MitchiLaser/Parallax/hardware/afe.kicad_sch

## KiCad design hardware/afe.kicad_sch (2025-06-27)

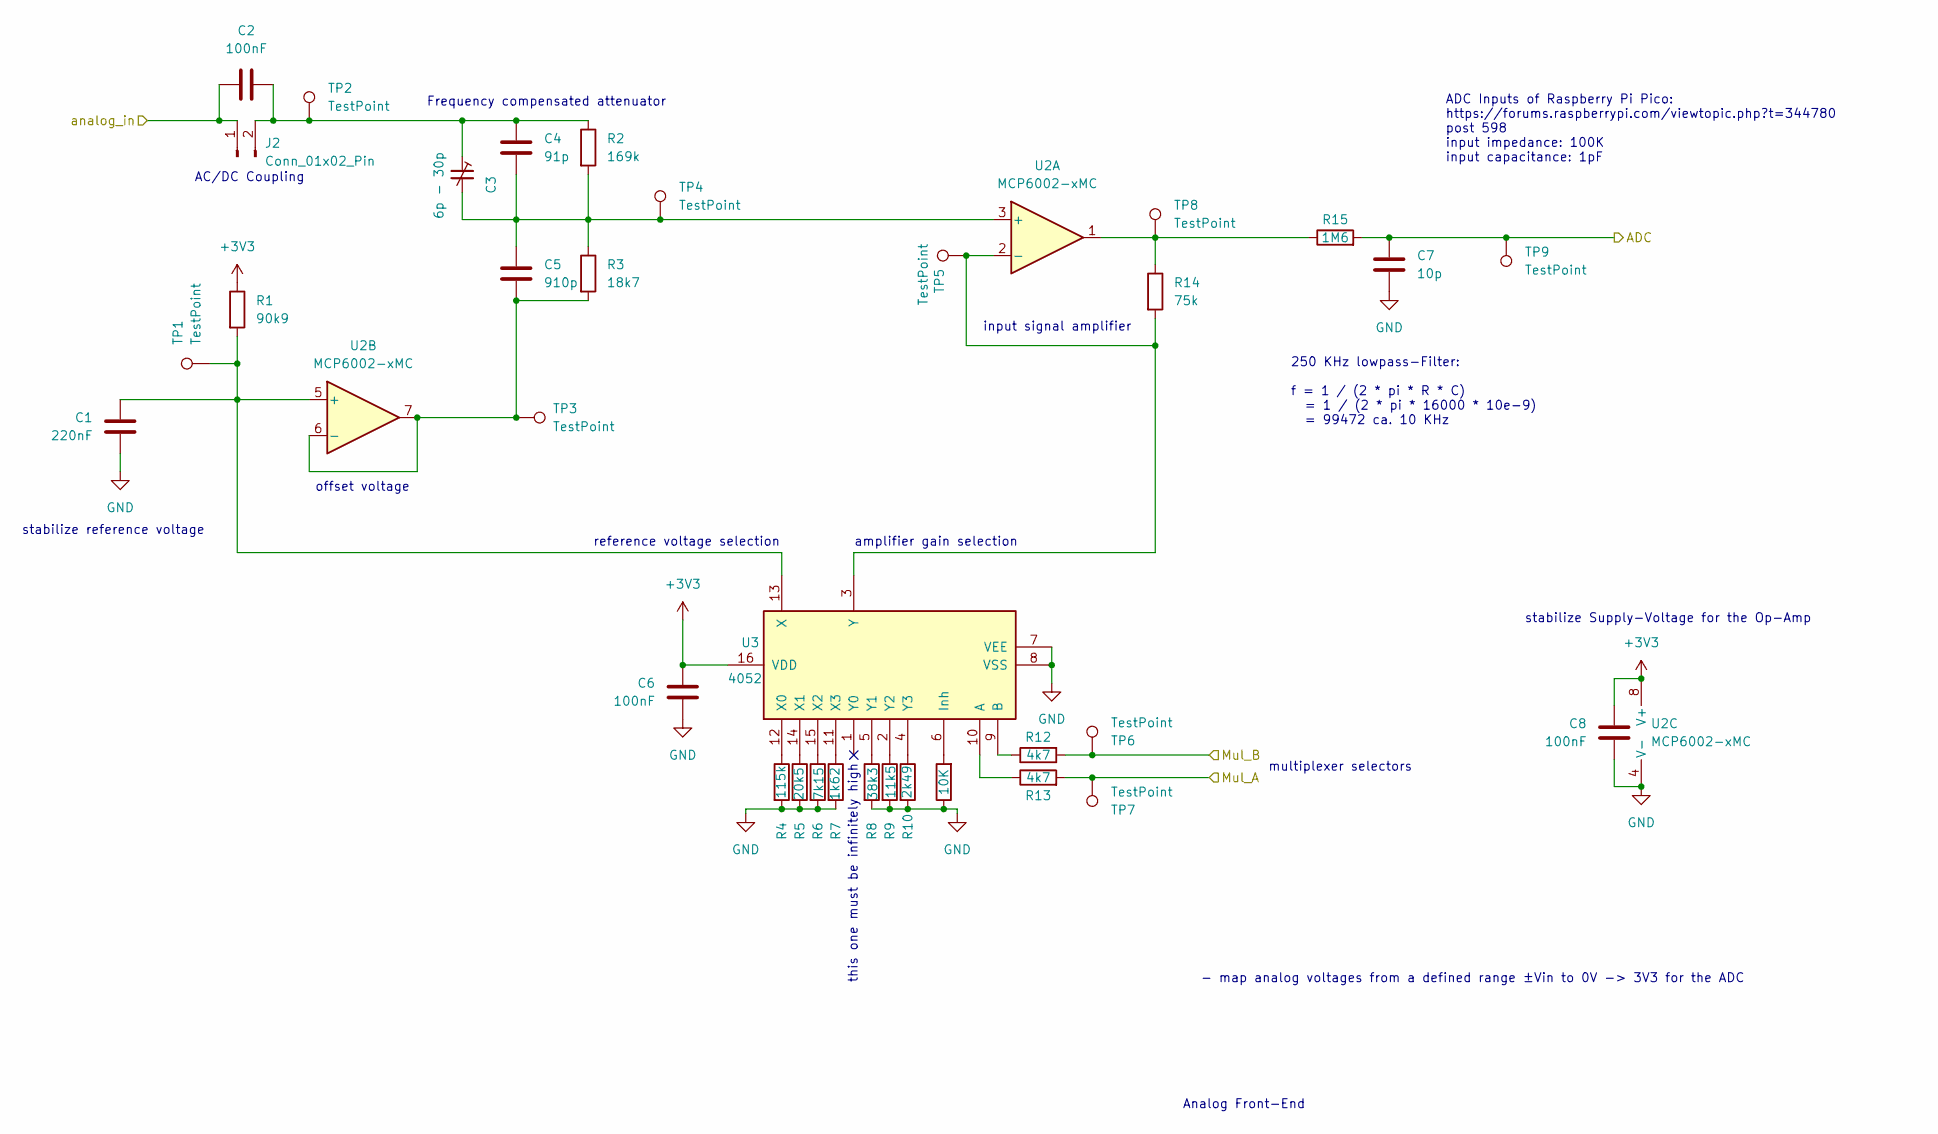
[picture p3: schematic afe.kicad_sch]

Parts:
C1: 220nF; C_0603_1608Metric
C2, C6, C8: 100nF; C_0603_1608Metric
C3: 6p - 30p; c_trim_D6mm_P5mm_1
C4: 91p; C_0603_1608Metric
C5: 910p; C_0603_1608Metric
C7: 10p; C_0603_1608Metric
J2: Conn_01x02_Pin; PinHeader_1x02_P2.54mm_Vertical
R1: 90k9; R_0603_1608Metric
R2: 169k; R_0603_1608Metric
R3: 18k7; R_0603_1608Metric
R4: 115k; R_0603_1608Metric
R5: 20k5; R_0603_1608Metric
R6: 7k15; R_0603_1608Metric
R7: 1k62; R_0603_1608Metric
R8: 38k3; R_0603_1608Metric
R9: 11k5; R_0603_1608Metric
R10: 2k49; R_0603_1608Metric
R11: 10K; R_0603_1608Metric
R12, R13: 4k7; R_0603_1608Metric
R14: 75k; R_0603_1608Metric
R15: 1M6; R_0603_1608Metric
TP1, TP2, TP3, TP4, TP5, TP6, TP7, TP8, TP9: TestPoint; TestPoint_Pad_D1.5mm
U2: MCP6002-xMC; DFN-8-1EP_3x2mm_P0.5mm_EP1.75x1.45mm
U3: 4052; SSOP-16_5.3x6.2mm_P0.65mm

Connections:
+3V3: C6.1, C8.1, R1.1, U2.8 (V+), U3.16 (VDD)
ADC: C7.1, R15.2, TP9.1
GND: C1.2, C6.2, C7.2, C8.2, R4.2, R5.2, R6.2, R7.2, R8.2, R9.2, R10.2, R11.1, U2.4 (V-), U2.9 (V-), U3.7 (VEE), U3.8 (VSS)
Mul_A: R13.2, TP7.1
Mul_B: R12.2, TP6.1
unnamed: C1.1, R1.2, TP1.1, U2.5 (+), U3.13 (X)
unnamed: C2.2, C3.1, C4.1, J2.2, R2.1, TP2.1
unnamed: C3.2, C4.2, C5.1, R2.2, R3.1, TP4.1, U2.3 (+)
unnamed: C5.2, R3.2, TP3.1, U2.6 (-), U2.7
unnamed: R4.1, U3.12 (X0)
unnamed: R5.1, U3.14 (X1)
unnamed: R6.1, U3.15 (X2)
unnamed: R7.1, U3.11 (X3)
unnamed: R8.1, U3.5 (Y1)
unnamed: R9.1, U3.2 (Y2)
unnamed: R10.1, U3.4 (Y3)
unnamed: R11.2, U3.6 (Inh)
unnamed: R12.1, U3.9 (B)
unnamed: R13.1, U3.10 (A)
unnamed: R14.1, R15.1, TP8.1, U2.1
unnamed: R14.2, TP5.1, U2.2 (-), U3.3 (Y)
analog_in: C2.1, J2.1

Notes on the sheet:
offset voltage
250 KHz lowpass-Filter: f = 1 / (2 * pi * R * C) = 1 / (2 * pi * 16000 * 10e-9) = 99472 ca. 10 KHz
- map analog voltages from a defined range ±Vin to 0V -> 3V3 for the ADC
ADC Inputs of Raspberry Pi Pico: https://forums.raspberrypi.com/viewtopic.php?t=344780 post 598 input impedance: 100K input capacitance: 1pF
reference voltage selection
AC/DC Coupling
Frequency compensated attenuator
input signal amplifier
this one must be infinitely high
amplifier gain selection
Analog Front-End
stabilize Supply-Voltage for the Op-Amp
multiplexer selectors
stabilize reference voltage
