MitchiLaser/Parallax/hardware/awg.kicad_sch

## KiCad design hardware/awg.kicad_sch (2025-06-20)

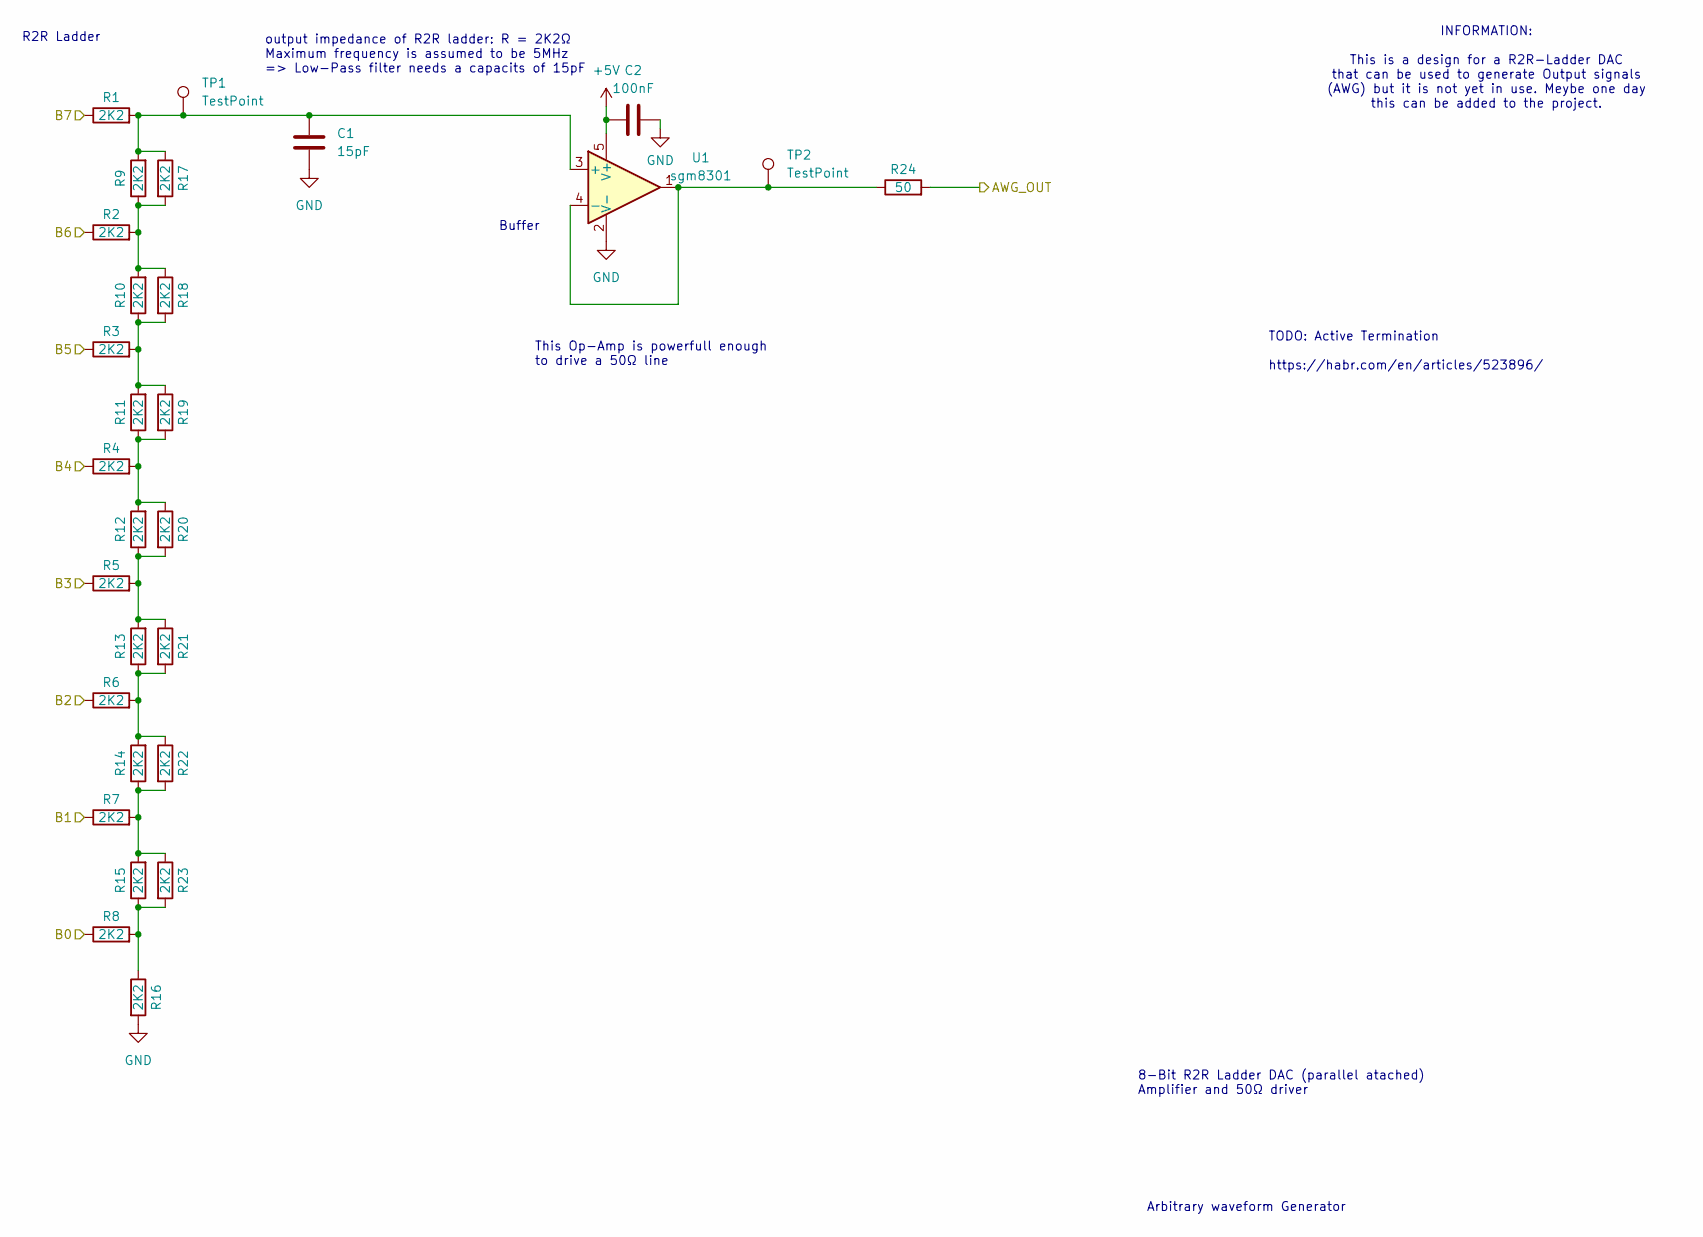
[picture p4: schematic awg.kicad_sch]

Parts:
C1: 15pF; C_0805_2012Metric_Pad1.18x1.45mm_HandSolder
C2: 100nF; C_0805_2012Metric_Pad1.18x1.45mm_HandSolder
R1, R2, R3, R4, R5, R6, R7, R8, R9, R10, R11, R12, R13, R14, R15, R16, R17, R18, R19, R20, R21, R22, R23: 2K2; R_0805_2012Metric_Pad1.20x1.40mm_HandSolder
R24: 50; R_0805_2012Metric_Pad1.20x1.40mm_HandSolder
TP1, TP2: TestPoint; TestPoint_Pad_D1.5mm
U1: sgm8301; SOT-23-5

Connections:
+5V: C2.1, U1.5 (V+)
AWG_OUT: R24.2
B0: R8.1
B1: R7.1
B2: R6.1
B3: R5.1
B4: R4.1
B5: R3.1
B6: R2.1
B7: R1.1
GND: C1.1, C2.2, R16.2, U1.2 (V-)
unnamed: C1.2, R1.2, R9.2, R17.1, TP1.1, U1.3 (+)
unnamed: R3.2, R10.1, R11.2, R18.2, R19.1
unnamed: R2.2, R9.1, R10.2, R17.2, R18.1
unnamed: R4.2, R11.1, R12.2, R19.2, R20.1
unnamed: R5.2, R12.1, R13.2, R20.2, R21.1
unnamed: R6.2, R13.1, R14.2, R21.2, R22.1
unnamed: R7.2, R14.1, R15.2, R22.2, R23.1
unnamed: R8.2, R15.1, R16.1, R23.2
unnamed: R24.1, TP2.1, U1.1, U1.4 (-)

Notes on the sheet:
R2R Ladder
Buffer
Arbitrary waveform Generator
TODO: Active Termination https://habr.com/en/articles/523896/
8-Bit R2R Ladder DAC (parallel atached) Amplifier and 50Ω driver
This Op-Amp is powerfull enough to drive a 50Ω line
INFORMATION: This is a design for a R2R-Ladder DAC that can be used to generate Output signals (AWG) but it is not yet in use. Meybe one day this can be added to the project.
output impedance of R2R ladder: R = 2K2Ω Maximum frequency is assumed to be 5MHz => Low-Pass filter needs a capacits of 15pF
