MitchiLaser/Parallax/hardware/parallax.kicad_sch

## KiCad design hardware/parallax.kicad_sch (2025-06-26)

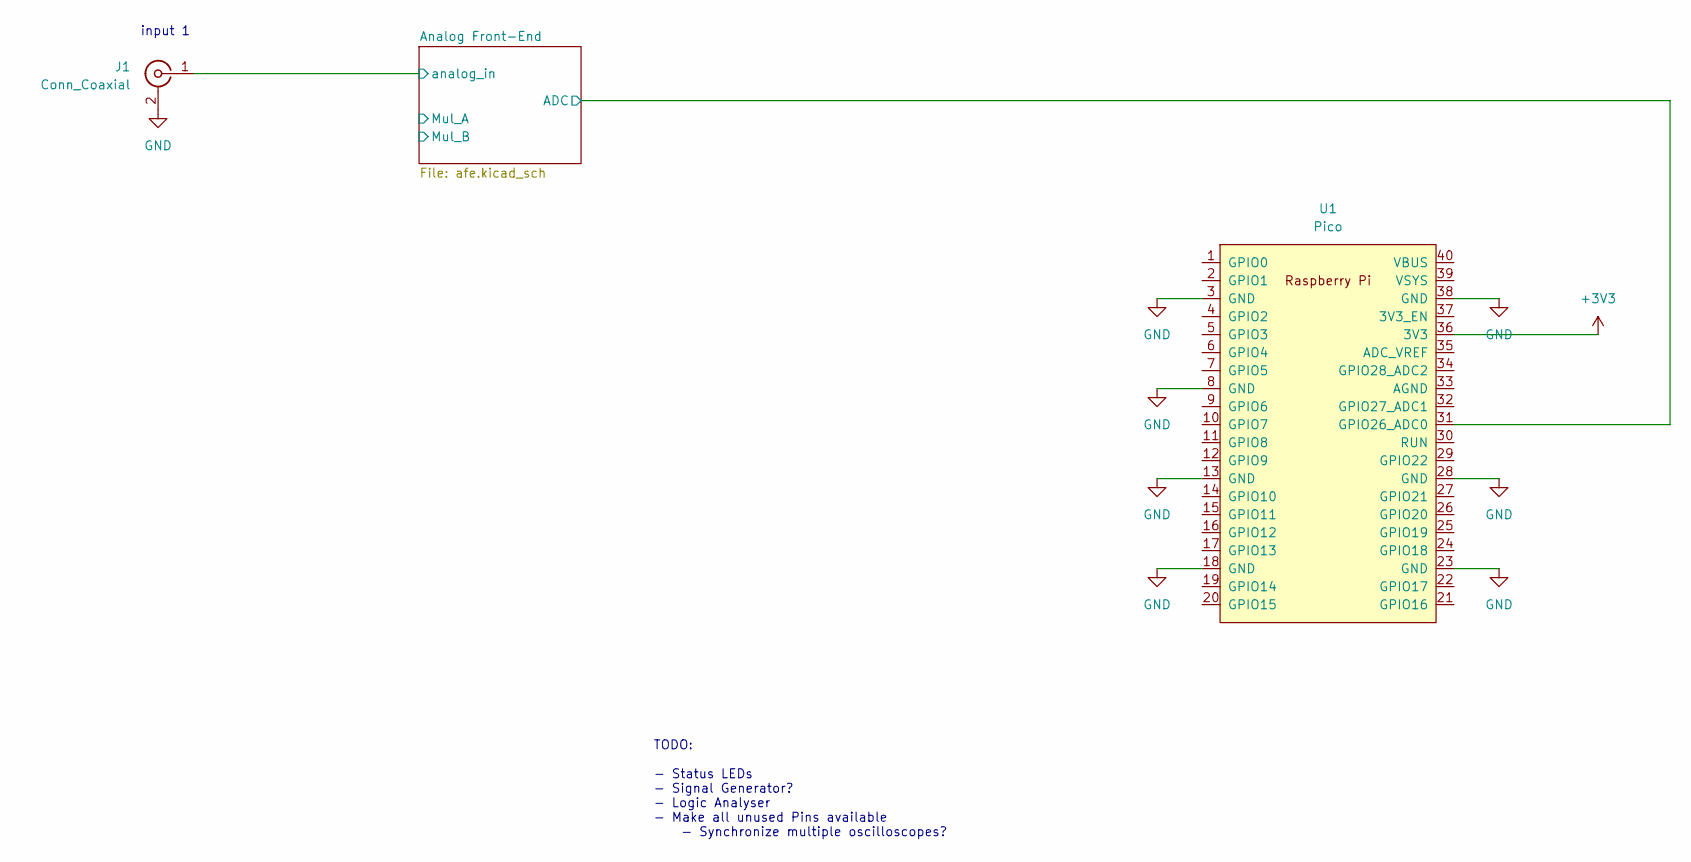
[picture p5: schematic parallax.kicad_sch]

Parts:
J1: Conn_Coaxial; BNC_Amphenol_B6252HB-NPP3G-50_Horizontal
U1: Pico; RaspberryPi_Pico_Common_Unspecified

Connections:
+3V3: U1.36 (3V3)
ADC: U1.31 (GPIO26_ADC0)
GND: J1.2 (Ext), U1.3 (GND), U1.8 (GND), U1.13 (GND), U1.18 (GND), U1.23 (GND), U1.28 (GND), U1.38 (GND)
analog_in: J1.1 (In)

Notes on the sheet:
input 1
TODO: - Status LEDs - Signal Generator? - Logic Analyser - Make all unused Pins available - Synchronize multiple oscilloscopes?
